Leeianiop/TimeyBot/PCB/TimeyBotSCH.kicad_sch

## KiCad design PCB/TimeyBotSCH.kicad_sch (2026-06-14)

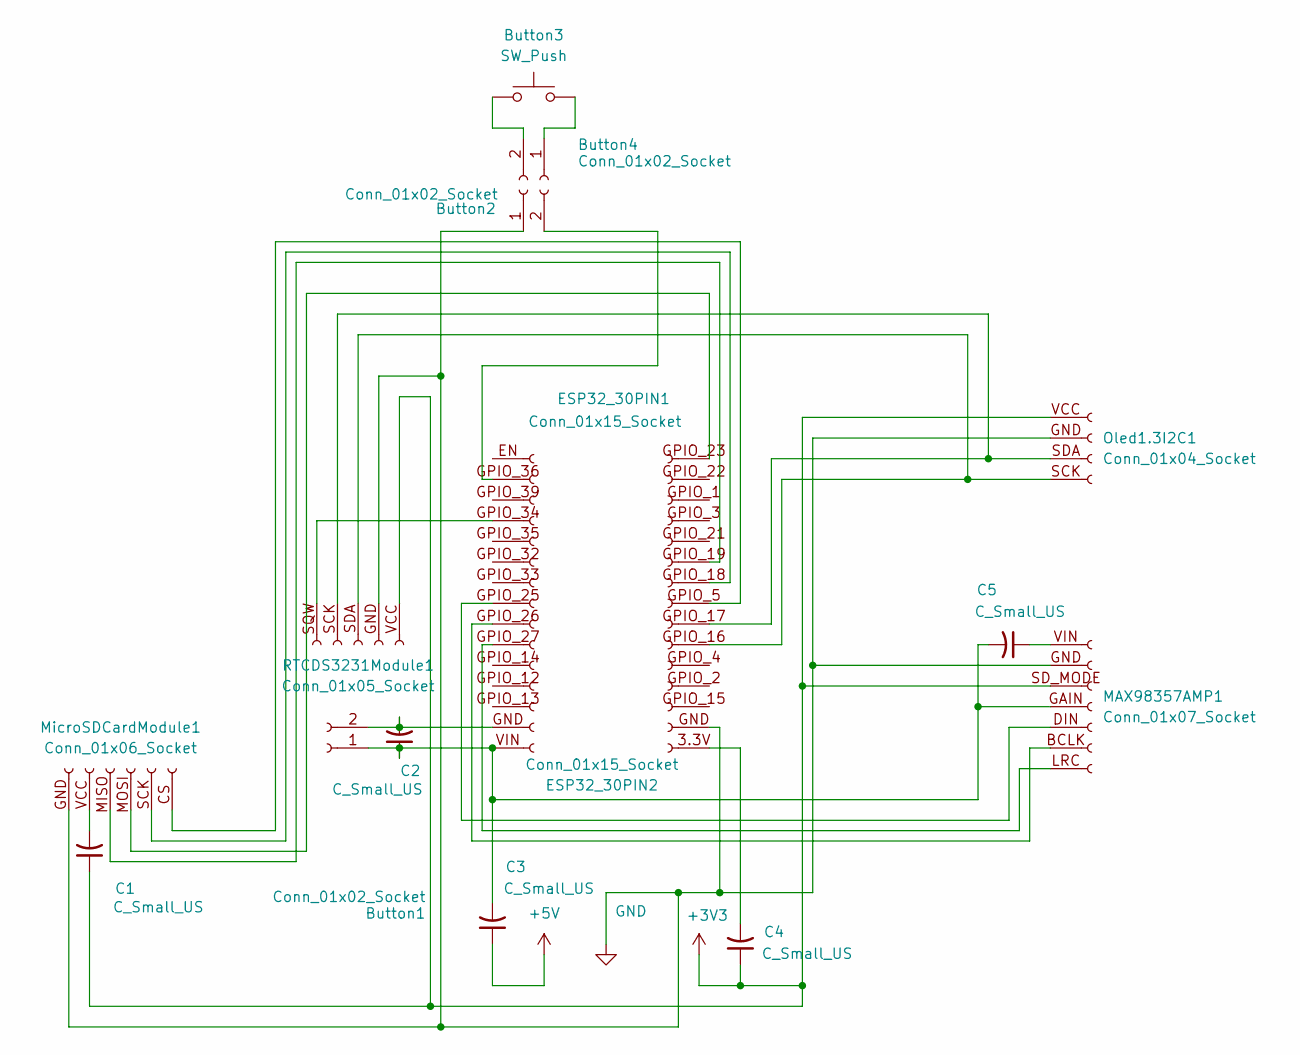
[picture p14: schematic TimeyBotSCH.kicad_sch]

Parts:
Button1, Button2, Button4: Conn_01x02_Socket; PinHeader_1x02_P2.54mm_Vertical
Button3: SW_Push; SW_PUSH-12mm
C1, C2, C3, C4, C5: C_Small_US; C_0805_2012Metric_Pad1.18x1.45mm_HandSolder
ESP32_30PIN1, ESP32_30PIN2: Conn_01x15_Socket; PinSocket_1x15_P2.54mm_Vertical
MAX98357AMP1: Conn_01x07_Socket; PinHeader_1x07_P2.54mm_Vertical
MicroSDCardModule1: Conn_01x06_Socket; PinHeader_1x06_P2.54mm_Vertical
Oled1.3I2C1: Conn_01x04_Socket; PinHeader_1x04_P2.54mm_Vertical
RTCDS3231Module1: Conn_01x05_Socket; PinHeader_1x05_P2.54mm_Vertical

Connections:
+3V3: C1.1, C4.1, MAX98357AMP1.SD_MODE (Pin_3), Oled1.3I2C1.VCC (Pin_1), RTCDS3231Module1.VCC (Pin_1)
+5V: C3.1
GND: Button2.1, ESP32_30PIN2.GND (Pin_14), MAX98357AMP1.GND (Pin_2), MicroSDCardModule1.GND (Pin_1), Oled1.3I2C1.GND (Pin_2), RTCDS3231Module1.GND (Pin_2)
unnamed: Button1.1, C2.1, C3.2, C5.2, ESP32_30PIN1.VIN (Pin_15), MAX98357AMP1.GAIN (Pin_4)
unnamed: Button1.2, C2.2, ESP32_30PIN1.GND (Pin_14)
unnamed: Button2.2, ESP32_30PIN1.GPIO_36 (Pin_2)
unnamed: Button3.1, Button4.2
unnamed: Button3.2, Button4.1
unnamed: C1.2, MicroSDCardModule1.VCC (Pin_2)
unnamed: C4.2, ESP32_30PIN2.3.3V (Pin_15)
unnamed: C5.1, MAX98357AMP1.VIN (Pin_1)
unnamed: ESP32_30PIN1.GPIO_25 (Pin_8), MAX98357AMP1.DIN (Pin_5)
unnamed: ESP32_30PIN1.GPIO_26 (Pin_9), MAX98357AMP1.BCLK (Pin_6)
unnamed: ESP32_30PIN1.GPIO_27 (Pin_10), MAX98357AMP1.LRC (Pin_7)
unnamed: ESP32_30PIN1.GPIO_34 (Pin_4), RTCDS3231Module1.SQW (Pin_5)
unnamed: ESP32_30PIN2.GPIO_5 (Pin_8), MicroSDCardModule1.CS (Pin_6)
unnamed: ESP32_30PIN2.GPIO_16 (Pin_10), Oled1.3I2C1.SCK (Pin_4), RTCDS3231Module1.SDA (Pin_3)
unnamed: ESP32_30PIN2.GPIO_17 (Pin_9), Oled1.3I2C1.SDA (Pin_3), RTCDS3231Module1.SCK (Pin_4)
unnamed: ESP32_30PIN2.GPIO_18 (Pin_7), MicroSDCardModule1.SCK (Pin_5)
unnamed: ESP32_30PIN2.GPIO_19 (Pin_6), MicroSDCardModule1.MISO (Pin_3)
unnamed: ESP32_30PIN2.GPIO_23 (Pin_1), MicroSDCardModule1.MOSI (Pin_4)
